nabilBastaki/Pico-Handheld_Console/Hardware/KiCad_Lib/3dshapes/MountingHoleScrew3mm.step

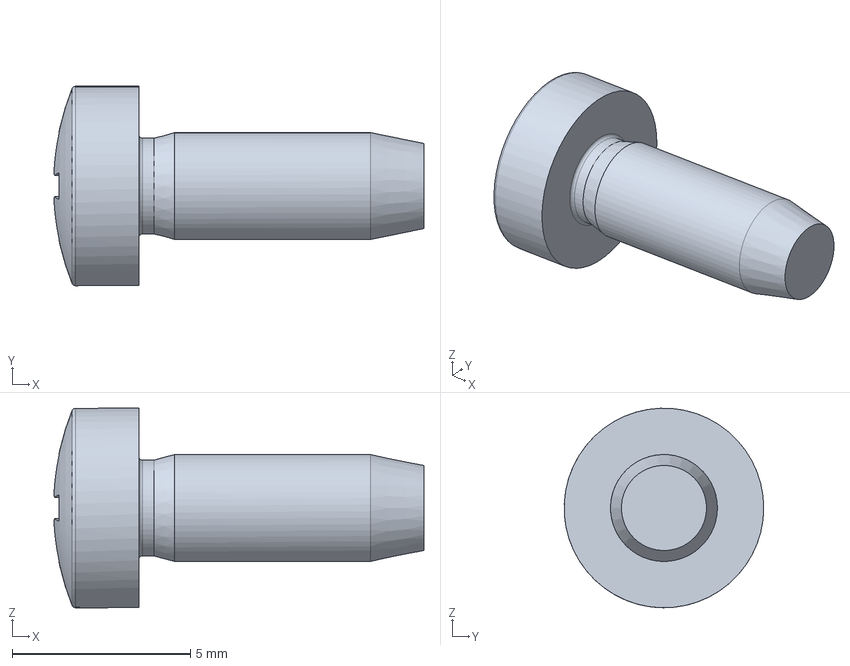
[picture p16: CAD file, 2026-03-19]
Hardware/KiCad_Lib/3dshapes/MountingHoleScrew3mm.step
10.4 x 5.60 x 5.60 mm
